watterott/MI0283QT-Adapter/firmware/lcd_font8x8.c

#include <stdint.h>
#include "lcd_font8x8.h"


//0x20 - 0xFF
const uint8_t fontdata[] = 
{
  0x00,0x00,0x00,0x00,0x00,0x00,0x00,0x00, // 0x20
  0x30,0x78,0x78,0x30,0x30,0x00,0x30,0x00, // 0x21
  0x6C,0x6C,0x6C,0x00,0x00,0x00,0x00,0x00, // 0x22
  0x6C,0x6C,0xFE,0x6C,0xFE,0x6C,0x6C,0x00, // 0x23
  0x30,0x7C,0xC0,0x78,0x0C,0xF8,0x30,0x00, // 0x24
  0x00,0xC6,0xCC,0x18,0x30,0x66,0xC6,0x00, // 0x25
  0x38,0x6C,0x38,0x76,0xDC,0xCC,0x76,0x00, // 0x26
  0x60,0x60,0xC0,0x00,0x00,0x00,0x00,0x00, // 0x27
  0x18,0x30,0x60,0x60,0x60,0x30,0x18,0x00, // 0x28
  0x60,0x30,0x18,0x18,0x18,0x30,0x60,0x00, // 0x29
  0x00,0x66,0x3C,0xFF,0x3C,0x66,0x00,0x00, // 0x2A
  0x00,0x30,0x30,0xFC,0x30,0x30,0x00,0x00, // 0x2B
  0x00,0x00,0x00,0x00,0x00,0x70,0x30,0x60, // 0x2C
  0x00,0x00,0x00,0xFC,0x00,0x00,0x00,0x00, // 0x2D
  0x00,0x00,0x00,0x00,0x00,0x30,0x30,0x00, // 0x2E
  0x06,0x0C,0x18,0x30,0x60,0xC0,0x80,0x00, // 0x2F
  0x78,0xCC,0xDC,0xFC,0xEC,0xCC,0x78,0x00, // 0x30
  0x30,0xF0,0x30,0x30,0x30,0x30,0xFC,0x00, // 0x31
  0x78,0xCC,0x0C,0x38,0x60,0xCC,0xFC,0x00, // 0x32
  0x78,0xCC,0x0C,0x38,0x0C,0xCC,0x78,0x00, // 0x33
  0x1C,0x3C,0x6C,0xCC,0xFE,0x0C,0x0C,0x00, // 0x34
  0xFC,0xC0,0xF8,0x0C,0x0C,0xCC,0x78,0x00, // 0x35
  0x38,0x60,0xC0,0xF8,0xCC,0xCC,0x78,0x00, // 0x36
  0xFC,0xCC,0x0C,0x18,0x30,0x60,0x60,0x00, // 0x37
  0x78,0xCC,0xCC,0x78,0xCC,0xCC,0x78,0x00, // 0x38
  0x78,0xCC,0xCC,0x7C,0x0C,0x18,0x70,0x00, // 0x39
  0x00,0x00,0x30,0x30,0x00,0x30,0x30,0x00, // 0x3A
  0x00,0x00,0x30,0x30,0x00,0x70,0x30,0x60, // 0x3B
  0x18,0x30,0x60,0xC0,0x60,0x30,0x18,0x00, // 0x3C
  0x00,0x00,0xFC,0x00,0xFC,0x00,0x00,0x00, // 0x3D
  0x60,0x30,0x18,0x0C,0x18,0x30,0x60,0x00, // 0x3E
  0x78,0xCC,0x0C,0x18,0x30,0x00,0x30,0x00, // 0x3F
  0x7C,0xC6,0xDE,0xDE,0xDE,0xC0,0x78,0x00, // 0x40
  0x30,0x78,0xCC,0xCC,0xFC,0xCC,0xCC,0x00, // 0x41
  0xFC,0x66,0x66,0x7C,0x66,0x66,0xFC,0x00, // 0x42
  0x3C,0x66,0xC0,0xC0,0xC0,0x66,0x3C,0x00, // 0x43
  0xFC,0x6C,0x66,0x66,0x66,0x6C,0xFC,0x00, // 0x44
  0xFE,0x62,0x68,0x78,0x68,0x62,0xFE,0x00, // 0x45
  0xFE,0x62,0x68,0x78,0x68,0x60,0xF0,0x00, // 0x46
  0x3C,0x66,0xC0,0xC0,0xCE,0x66,0x3E,0x00, // 0x47
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
};
