watterott/MI0283QT-Adapter/firmware/lcd_mi0283qt9.h

#ifndef _LCD_MI0283QT9_H_
#define _LCD_MI0283QT9_H_

#ifdef LCD_MI0283QT9


//----- DEFINES -----
#define LCD_WIDTH                      320
#define LCD_HEIGHT                     240

#define LCD_CMD_NOP                    0x00
#define LCD_CMD_RESET                  0x01
#define LCD_CMD_SLEEPIN                0x10
#define LCD_CMD_SLEEPOUT               0x11
#define LCD_CMD_PARTIAL_MODE           0x12
#define LCD_CMD_NORMAL_MODE            0x13
#define LCD_CMD_INV_OFF                0x20
#define LCD_CMD_INV_ON                 0x21
#define LCD_CMD_GAMMA                  0x26
#define LCD_CMD_DISPLAY_OFF            0x28
#define LCD_CMD_DISPLAY_ON             0x29
#define LCD_CMD_COLUMN                 0x2A
#define LCD_CMD_PAGE                   0x2B
#define LCD_CMD_WRITE                  0x2C
#define LCD_CMD_READ                   0x2E
#define LCD_CMD_PARTIAL_AREA           0x30
#define LCD_CMD_TEARING_OFF            0x34
#define LCD_CMD_TEARING_ON             0x35
#define LCD_CMD_MEMACCESS_CTRL         0x36
#define LCD_CMD_IDLE_OFF               0x38
#define LCD_CMD_IDLE_ON                0x39
#define LCD_CMD_PIXEL_FORMAT           0x3A
#define LCD_CMD_WRITE_CNT              0x3C
#define LCD_CMD_READ_CNT               0x3E
#define LCD_CMD_BRIGHTNESS             0x51
#define LCD_CMD_BRIGHTNESS_CTRL        0x53
#define LCD_CMD_RGB_CTRL               0xB0
#define LCD_CMD_FRAME_CTRL             0xB1 //normal mode
#define LCD_CMD_FRAME_CTRL_IDLE        0xB2 //idle mode
#define LCD_CMD_FRAME_CTRL_PART        0xB3 //partial mode
#define LCD_CMD_INV_CTRL               0xB4
#define LCD_CMD_DISPLAY_CTRL           0xB6
#define LCD_CMD_ENTRY_MODE             0xB7
#define LCD_CMD_POWER_CTRL1            0xC0
#define LCD_CMD_POWER_CTRL2            0xC1
#define LCD_CMD_VCOM_CTRL1             0xC5
#define LCD_CMD_VCOM_CTRL2             0xC7
#define LCD_CMD_POWER_CTRLA            0xCB
#define LCD_CMD_POWER_CTRLB            0xCF
#define LCD_CMD_POS_GAMMA              0xE0
#define LCD_CMD_NEG_GAMMA              0xE1
#define LCD_CMD_DRV_TIMING_CTRLA       0xE8
#define LCD_CMD_DRV_TIMING_CTRLB       0xEA
#define LCD_CMD_POWERON_SEQ_CTRL       0xED
#define LCD_CMD_ENABLE_3G              0xF2
#define LCD_CMD_INTERF_CTRL            0xF6
#define LCD_CMD_PUMP_RATIO_CTRL        0xF7


//----- PROTOTYPES -----
#define                                lcd_drawstop()
//void                                   lcd_drawstop(void); //empty function
void                                   lcd_draw(uint_least16_t color);
void                                   lcd_drawstart(void);
void                                   lcd_setarea(uint_least16_t x0, uint_least16_t y0, uint_least16_t x1, uint_least16_t y1);
uint_least32_t                         lcd_setbias(uint_least16_t o);
void                                   lcd_invert(uint_least8_t on);
void                                   lcd_power(uint_least8_t on);
void                                   lcd_reset(void);
void                                   lcd_wrdata16(uint_least16_t data);
void                                   lcd_wrdata8(uint_least8_t data);
void                                   lcd_wrcmd8(uint_least8_t cmd);
void                                   lcd_disable(void);
void                                   lcd_enable(void);


#endif //LCD_MI0283QT9

#endif //_LCD_MI0283QT9_H_
