watterott/MI0283QT-Adapter/firmware/lcd_font8x8.h

#ifndef _LCD_FONT8X8_H_
#define _LCD_FONT8X8_H_


//----- DEFINES -----
#define FONT_START                     0x20
#define FONT_WIDTH                     8
#define FONT_HEIGHT                    8


//----- GLOBALS -----
extern const uint8_t fontdata[];


#endif //_LCD_FONT8X8_H_
